c0pperdragon/A-VideoBoard/c64mod/quartus/ClockMultiplier.vhd

library ieee;
use ieee.numeric_std.all;
use ieee.std_logic_1164.all;

entity ClockMultiplier is	
	port (
		-- reference clock
		CLK25: in std_logic;		
		-- C64 cpu clock
		PHI0: in std_logic;
		-- 0: use input frequency for NTSC
		-- 1: use input frequency for PAL
		PAL: in std_logic;
		
		-- x16 times output clock
		CLK: out std_logic;
		
		-- auxilary pixel and subcarrier clock
		AUXPIXELCLOCK : out std_logic
	);	
end entity;


architecture immediate of ClockMultiplier is
   -- re-configuration inputs into the PLL
	signal CONFIGUPDATE : std_logic;
	signal SCANCLKENA : std_logic;
	signal SCANDATA: std_logic;
	-- high-speed clock to generate synchronous clock from. this is done
	-- with 4 coupled signals that are 0,45,90,135 degree phase shifted to give
	-- 8 usable edges.
	signal CLKA : std_logic;  
	signal CLKB : std_logic;
	signal CLKC : std_logic;
	signal CLKD : std_logic;

   component PLL252 is
	PORT
	(
		configupdate		: IN STD_LOGIC  := '0';
		inclk0		: IN STD_LOGIC  := '0';
		scanclk		: IN STD_LOGIC  := '1';
		scanclkena		: IN STD_LOGIC  := '0';
		scandata		: IN STD_LOGIC  := '0';
		c0		: OUT STD_LOGIC ;
		c1		: OUT STD_LOGIC ;
		c2		: OUT STD_LOGIC ;
		c3		: OUT STD_LOGIC ;
		scandataout		: OUT STD_LOGIC ;
		scandone		: OUT STD_LOGIC 
	);
	end component;
   component PLL262 is
	PORT
	(
		configupdate		: IN STD_LOGIC  := '0';
		inclk0		: IN STD_LOGIC  := '0';
		scanclk		: IN STD_LOGIC  := '1';
		scanclkena		: IN STD_LOGIC  := '0';
		scandata		: IN STD_LOGIC  := '0';
		c0		: OUT STD_LOGIC ;
		c1		: OUT STD_LOGIC ;
		c2		: OUT STD_LOGIC ;
		c3		: OUT STD_LOGIC ;
		scandataout		: OUT STD_LOGIC ;
		scandone		: OUT STD_LOGIC 
	);
	end component;
		
begin		
	subdividerpll: PLL252 port map ( CONFIGUPDATE, CLK25, CLK25, SCANCLKENA, SCANDATA, CLKA, CLKB, CLKC, CLKD, open,open );   -- use with PAL
--	subdividerpll: PLL262 port map ( CONFIGUPDATE, CLK25, CLK25, SCANCLKENA, SCANDATA, CLKA, CLKB, CLKC, CLKD, open,open );   -- use with NTSC
	
	-- generate the 16 times CPU clock
	process (PHI0, CLKA, CLKB, CLKC, CLKD)
		-- having 8 versions of the circuit running slightly 
		-- time-shifted
		variable counter0 : unsigned(3 downto 0) := "0000";
		variable counter1 : unsigned(3 downto 0) := "0000";
		variable counter2 : unsigned(3 downto 0) := "0000";
		variable counter3 : unsigned(3 downto 0) := "0000";
		variable counter4 : unsigned(3 downto 0) := "0000";
		variable counter5 : unsigned(3 downto 0) := "0000";
		variable counter6 : unsigned(3 downto 0) := "0000";
		variable counter7 : unsigned(3 downto 0) := "0000";
		variable in0_clk : std_logic := '0'; 
		variable in1_clk : std_logic := '0'; 		
		variable in2_clk : std_logic := '0'; 		
		variable in3_clk : std_logic := '0'; 		
		variable in4_clk : std_logic := '0'; 
		variable in5_clk : std_logic := '0'; 		
		variable in6_clk : std_logic := '0'; 		
		variable in7_clk : std_logic := '0'; 		
		variable prev0_clk : std_logic := '0';
		variable prev1_clk : std_logic := '0';		
		variable prev2_clk : std_logic := '0';		
		variable prev3_clk : std_logic := '0';	
		variable prev4_clk : std_logic := '0';
		variable prev5_clk : std_logic := '0';		
		variable prev6_clk : std_logic := '0';		
		variable prev7_clk : std_logic := '0';	
			
		variable bits : std_logic_vector(3 downto 0);
		constant reset: unsigned(3 downto 0) := "1000";
	begin
	
		if rising_edge(CLKA) then
			if in0_clk='0' and prev0_clk='1' then 
				counter0 := reset; 
			else
				counter0 := counter0+1;
			end if;
			prev0_clk := in0_clk;
			in0_clk := PHI0;  
		end if;
		if rising_edge(CLKB) then
			if in1_clk='0' and prev1_clk='1' then 
				counter1 := reset; 
			else
				counter1 := counter1+1;
			end if;
			prev1_clk := in1_clk;
			in1_clk := PHI0;  
		end if;
		if rising_edge(CLKC) then
			if in2_clk='0' and prev2_clk='1' then 
				counter2 := reset; 
			else
				counter2 := counter2+1;
			end if;
			prev2_clk := in2_clk;
			in2_clk := PHI0;  
		end if;
		if rising_edge(CLKD) then
			if in3_clk='0' and prev3_clk='1' then 
				counter3 := reset; 
			else
				counter3 := counter3+1;
			end if;
			prev3_clk := in3_clk;
			in3_clk := PHI0;  
		end if;
		if falling_edge(CLKA) then
			if in4_clk='0' and prev4_clk='1' then 
				counter4 := reset; 
			else
				counter4 := counter4+1;
			end if;
			prev4_clk := in4_clk;
			in4_clk := PHI0;  
		end if;
		if falling_edge(CLKB) then
			if in5_clk='0' and prev5_clk='1' then 
				counter5 := reset; 
			else
				counter5 := counter5+1;
			end if;
			prev5_clk := in5_clk;
			in5_clk := PHI0;  
		end if;
		if falling_edge(CLKC) then
			if in6_clk='0' and prev6_clk='1' then 
				counter6 := reset; 
			else
				counter6 := counter6+1;
			end if;
			prev6_clk := in6_clk;
			in6_clk := PHI0;  
		end if;
		if falling_edge(CLKD) then
			if in7_clk='0' and prev7_clk='1' then 
				counter7 := reset; 
			else
				counter7 := counter7+1;
			end if;
			prev7_clk := in7_clk;
			in7_clk := PHI0;  
		end if;
		
      -- merge clock counters asynchronously
		bits:= std_logic_vector
		(	   counter0 
			or counter1 
		   or counter2 
			or counter3
			or counter4 
		   or counter5 
			or counter6
			or counter7
		);
		CLK <= bits(3);
	end process;

	
	-- watch the PAL / NTSC selector and reprogramm PLL if necessary
	process (CLK25)
	type config_t is array (0 to 143) of std_logic;
	constant CONFIG262 : config_t :=  
	(	'0','0','0','0','1','1','0','0','0','0',
		'0','0','0','0','0','0','0','1','1','0',
		'0','0','0','0','0','0','0','0','0','0',
		'0','0','0','0','0','0','0','0','0','0',
		'0','1','0','1','1','1','0','0','0','0',
		'1','0','1','0','0','0','0','0','0','0',
		'0','0','1','0','0','0','0','0','0','0',
		'0','1','0','0','0','0','0','0','0','0',
		'1','0','0','0','0','0','0','0','0','1',
		'0','0','0','0','0','0','0','0','1','0',
		'0','0','0','0','0','0','0','1','0','0',
		'0','0','0','0','0','0','1','0','0','0',
		'0','0','0','0','0','1','1','0','0','0',
		'0','0','0','0','0','0','0','0','0','0',
		'0','0','0','0' 
	);
	constant CONFIG252 : config_t :=  
	(	'0','0','0','0','0','1','0','0','0','1',
		'0','0','0','0','0','0','0','1','0','0',
		'0','0','0','0','0','1','1','1','0','0',
		'0','0','0','0','1','0','0','0','1','1',
		'1','1','1','1','0','0','0','1','1','1',
		'1','1','1','0','0','0','0','0','0','0',
		'0','1','1','1','0','0','0','0','0','0',
		'1','0','0','0','0','0','0','0','0','1',
		'1','1','0','0','0','0','0','0','1','0',
		'0','0','0','0','0','0','0','1','1','1',
		'0','0','0','0','0','0','1','0','0','0',
		'0','0','0','0','0','1','1','1','0','0',
		'0','0','0','0','1','0','1','0','0','0',
		'0','0','0','0','0','0','0','0','0','0',
		'0','0','0','0' 
	);
	variable checkdelay:integer range 0 to 100000 := 0;
	variable programmedPAL : std_logic := '1';
	variable programcounter:integer range 0 to 255 := 0;
	variable out_configupdate : std_logic := '0';
	variable out_scanclkena : std_logic := '0';
	variable out_scandata : std_logic := '0';
	begin
		if rising_edge(CLK25) then
			out_scanclkena := '0';
			out_scandata := '0';
			out_configupdate := '0';

			-- for safety: short delay after power-up before checking
			if checkdelay/=100000 then
				checkdelay := checkdelay+1;
				
			-- when re-programming has not started, keep a watch on the 
			-- PAL mode signal and start programming if needed
			elsif programcounter=0 then
				if PAL/=programmedPAL then
					programmedPAL := PAL;
					out_scanclkena := '1';
					if programmedPAL='0' then
						out_scandata := CONFIG262(143);
					else
						out_scandata := CONFIG252(143);
					end if;
					programcounter := 1;
				end if;			
			elsif programcounter<=143 then
				out_scanclkena := '1';
				if programmedPAL='0' then
					out_scandata := CONFIG262(143-programcounter);
				else
					out_scandata := CONFIG252(143-programcounter);	
				end if;
				programcounter := programcounter+1;				
			elsif programcounter<150 then
				programcounter := programcounter+1;				
			elsif programcounter=150 then
				out_configupdate := '1';
				programcounter := 0;				
			end if;
		end if;
		
		CONFIGUPDATE <= out_configupdate;
		SCANCLKENA <= out_scanclkena;
		SCANDATA <= out_scandata;
	end process;
	
	-- generate a pixel clock and a subcarrier clock that can be used to drive the VIC
	-- instead of the shaky built-in oscillator (very special use only)
	process (CLKA)
		variable counter : unsigned(4 downto 0) := "00000";
	begin
		if rising_edge(CLKA) then
			counter := counter+1;
		end if;
		AUXPIXELCLOCK <= counter(4);
	end process;
	
	
end immediate;
